hekkelek/amiga-keyboard/fw/matrix.h

/*! *******************************************************************************************************
* Copyright (c) 2018 Kristóf Szabolcs Horváth
*
* All rights reserved
*
* \file matrix.h
*
* \brief Keyboard matrix interface
*
* \author Kristóf Sz. Horváth
*
**********************************************************************************************************/

#ifndef MATRIX_H_INCLUDED
#define MATRIX_H_INCLUDED

//--------------------------------------------------------------------------------------------------------/
// Include files
//--------------------------------------------------------------------------------------------------------/


//--------------------------------------------------------------------------------------------------------/
// Definitions
//--------------------------------------------------------------------------------------------------------/


//--------------------------------------------------------------------------------------------------------/
// Types
//--------------------------------------------------------------------------------------------------------/


//--------------------------------------------------------------------------------------------------------/
// Global functions
//--------------------------------------------------------------------------------------------------------/


//--------------------------------------------------------------------------------------------------------/
// Public functions
//--------------------------------------------------------------------------------------------------------/
void Matrix_Init( void );
void Matrix_Cycle( void );
void Matrix_Sample( void );


#endif // MATRIX_H_INCLUDED
/******************************<EOF>**********************************/
